INFERLab/AC_Waveform_Meter/images/Documentation Pictures/2018-07-11-145227_1280x1024_scrot.png

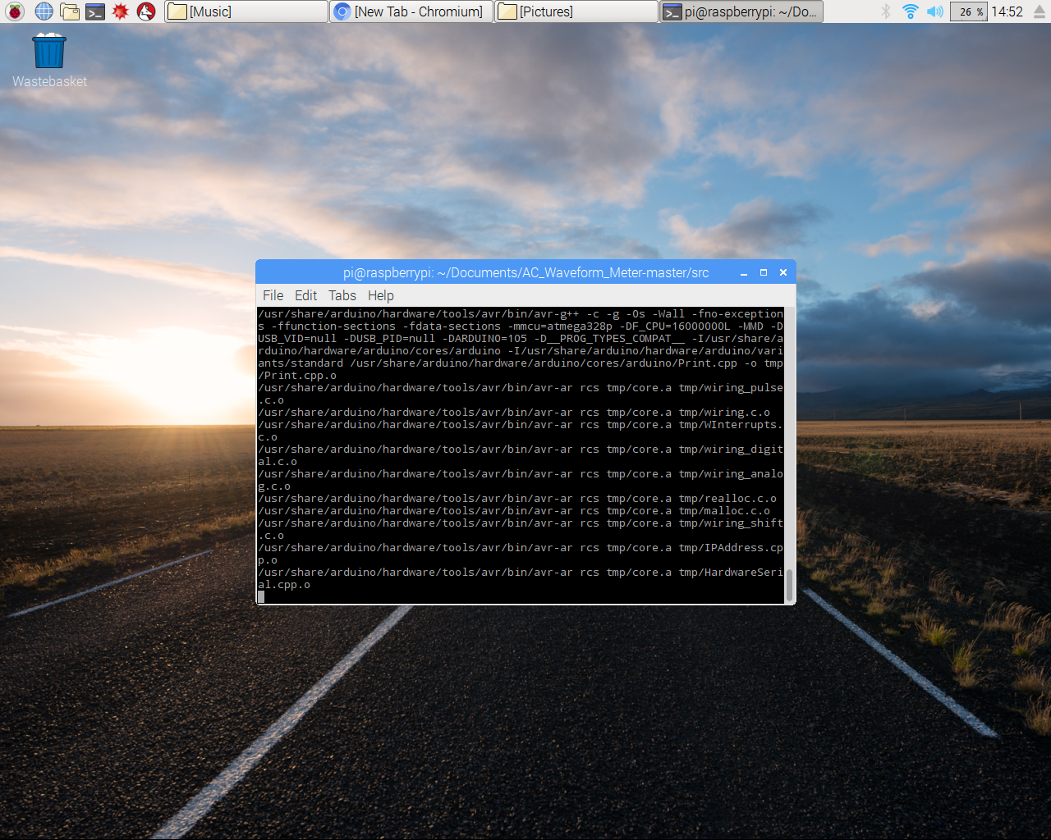
images/Documentation Pictures/2018-07-11-145227_1280x1024_scrot.png
