INFERLab/AC_Waveform_Meter/images/Documentation Pictures/IMAG1630.jpg

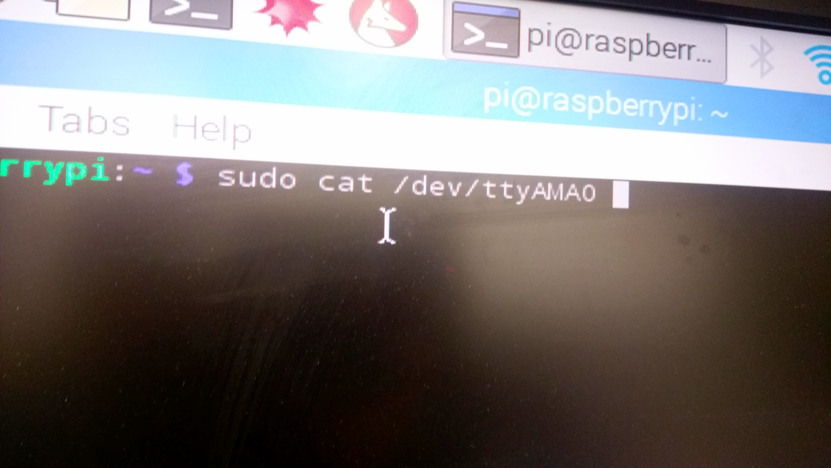
images/Documentation Pictures/IMAG1630.jpg
