INFERLab/AC_Waveform_Meter/images/Documentation Pictures/IMAG1632.jpg

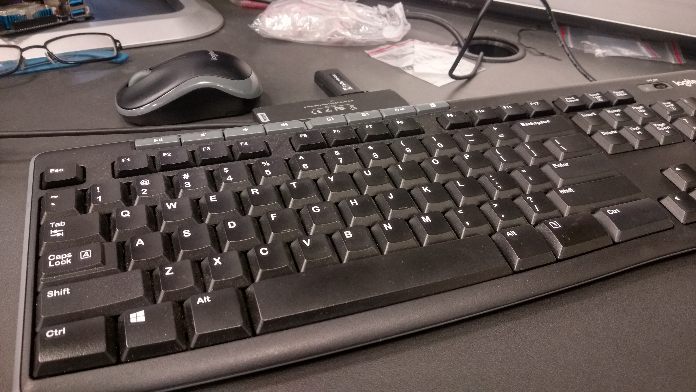
images/Documentation Pictures/IMAG1632.jpg
