INFERLab/AC_Waveform_Meter/images/Documentation Pictures/IMAG1634.jpg

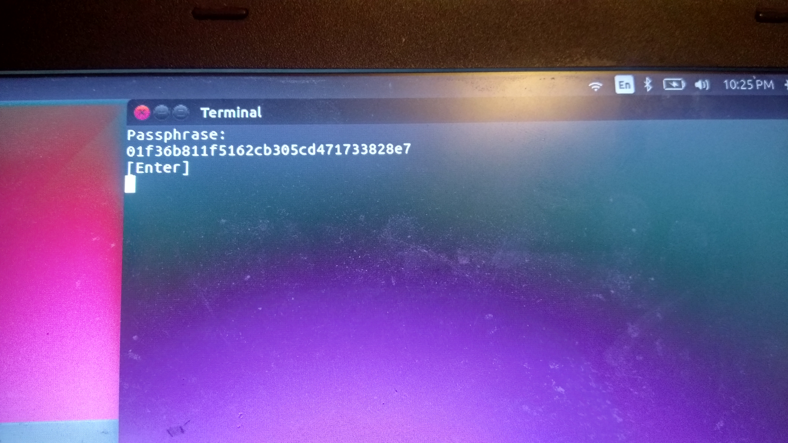
images/Documentation Pictures/IMAG1634.jpg
