INFERLab/AC_Waveform_Meter/images/Documentation Pictures/IMAG1636.jpg

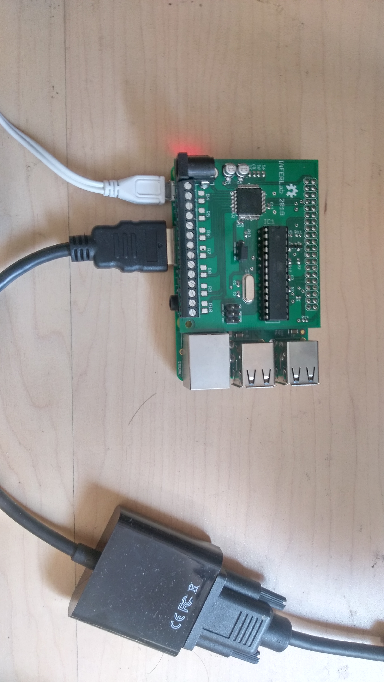
images/Documentation Pictures/IMAG1636.jpg
