INFERLab/AC_Waveform_Meter/images/Documentation Pictures/IMAG1638.jpg

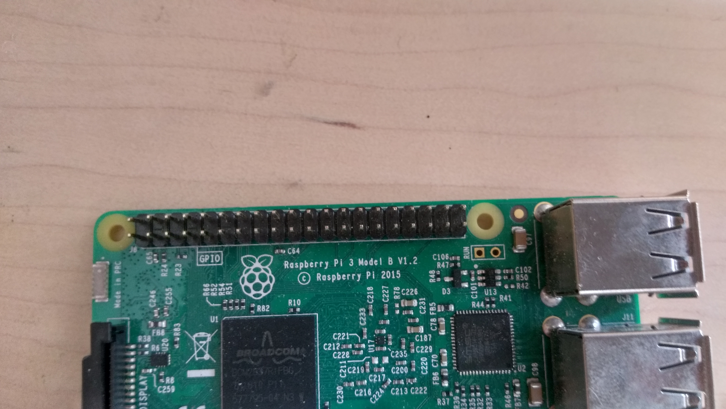
images/Documentation Pictures/IMAG1638.jpg
