INFERLab/AC_Waveform_Meter/images/Documentation Pictures/IMAG1640.jpg

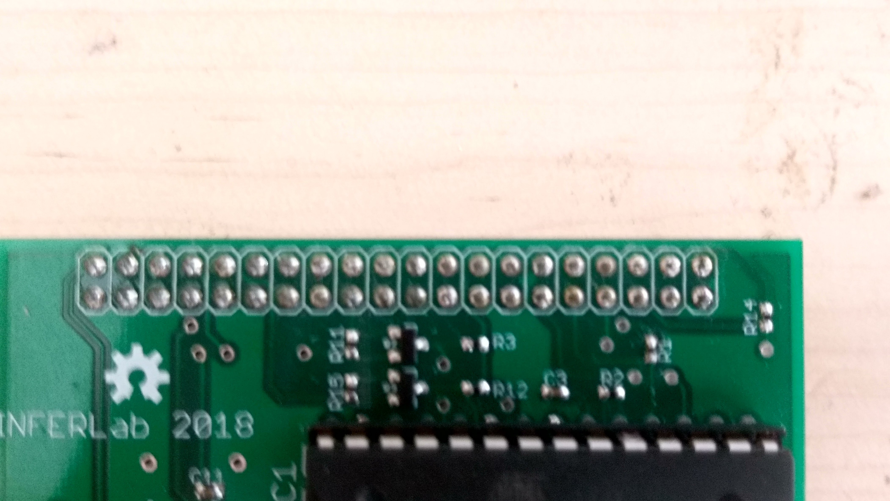
images/Documentation Pictures/IMAG1640.jpg
