INFERLab/AC_Waveform_Meter/images/Documentation Pictures/IMAG1641.jpg

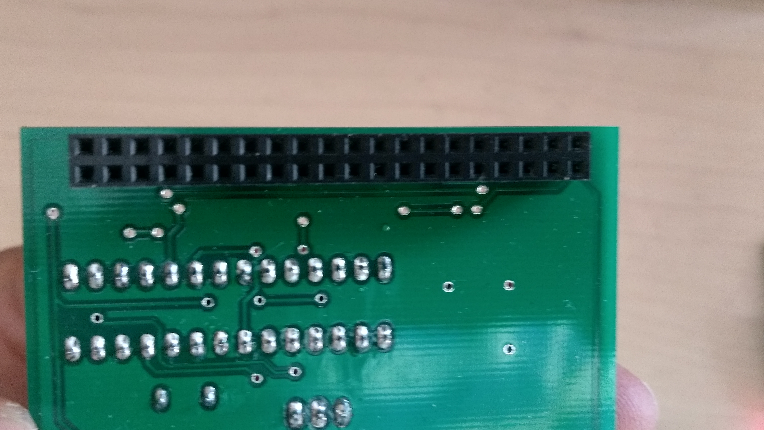
images/Documentation Pictures/IMAG1641.jpg
