INFERLab/AC_Waveform_Meter/images/Documentation Pictures/IMAG1643.jpg

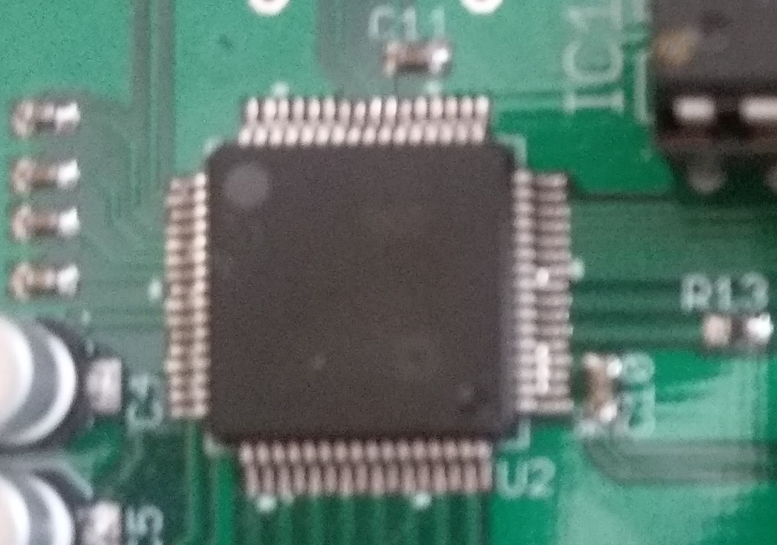
images/Documentation Pictures/IMAG1643.jpg
