INFERLab/AC_Waveform_Meter/images/Documentation Pictures/IMAG1644.jpg

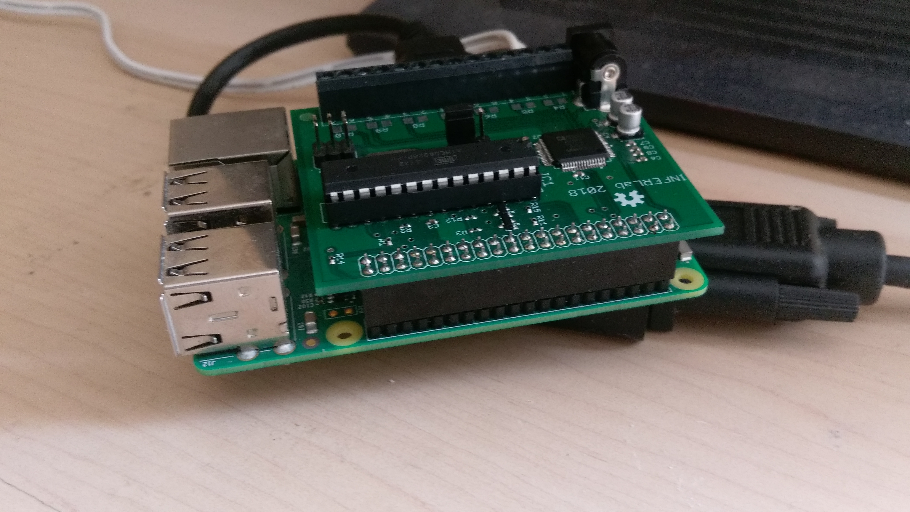
images/Documentation Pictures/IMAG1644.jpg
