INFERLab/AC_Waveform_Meter/images/Documentation Pictures/IMAG1645.jpg

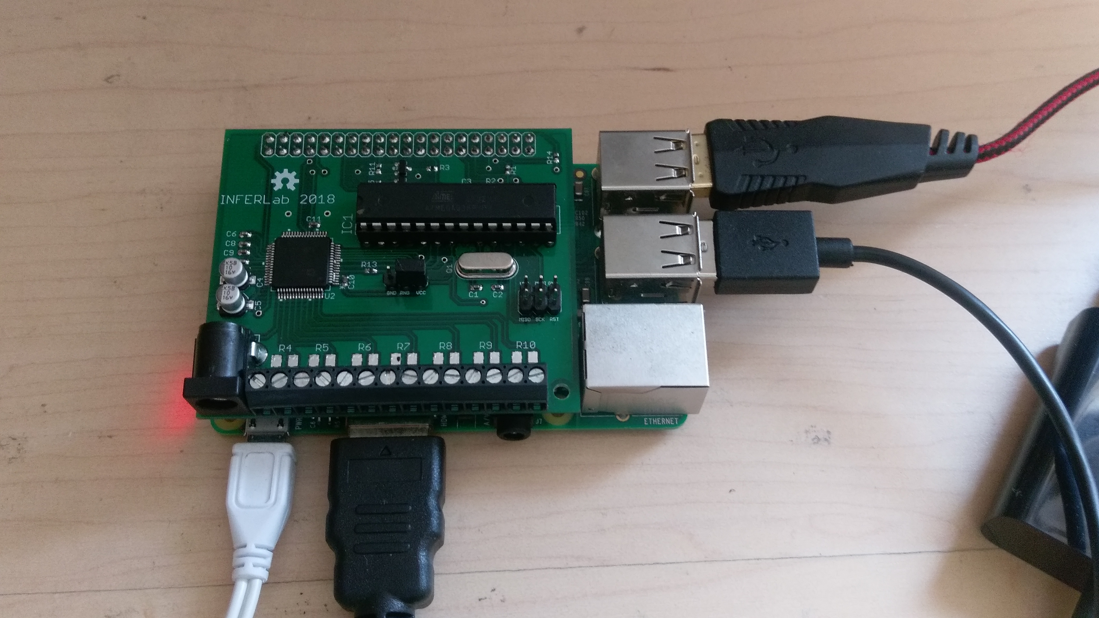
images/Documentation Pictures/IMAG1645.jpg
